Randagodron/satelyte/export/distortion_01_1.png

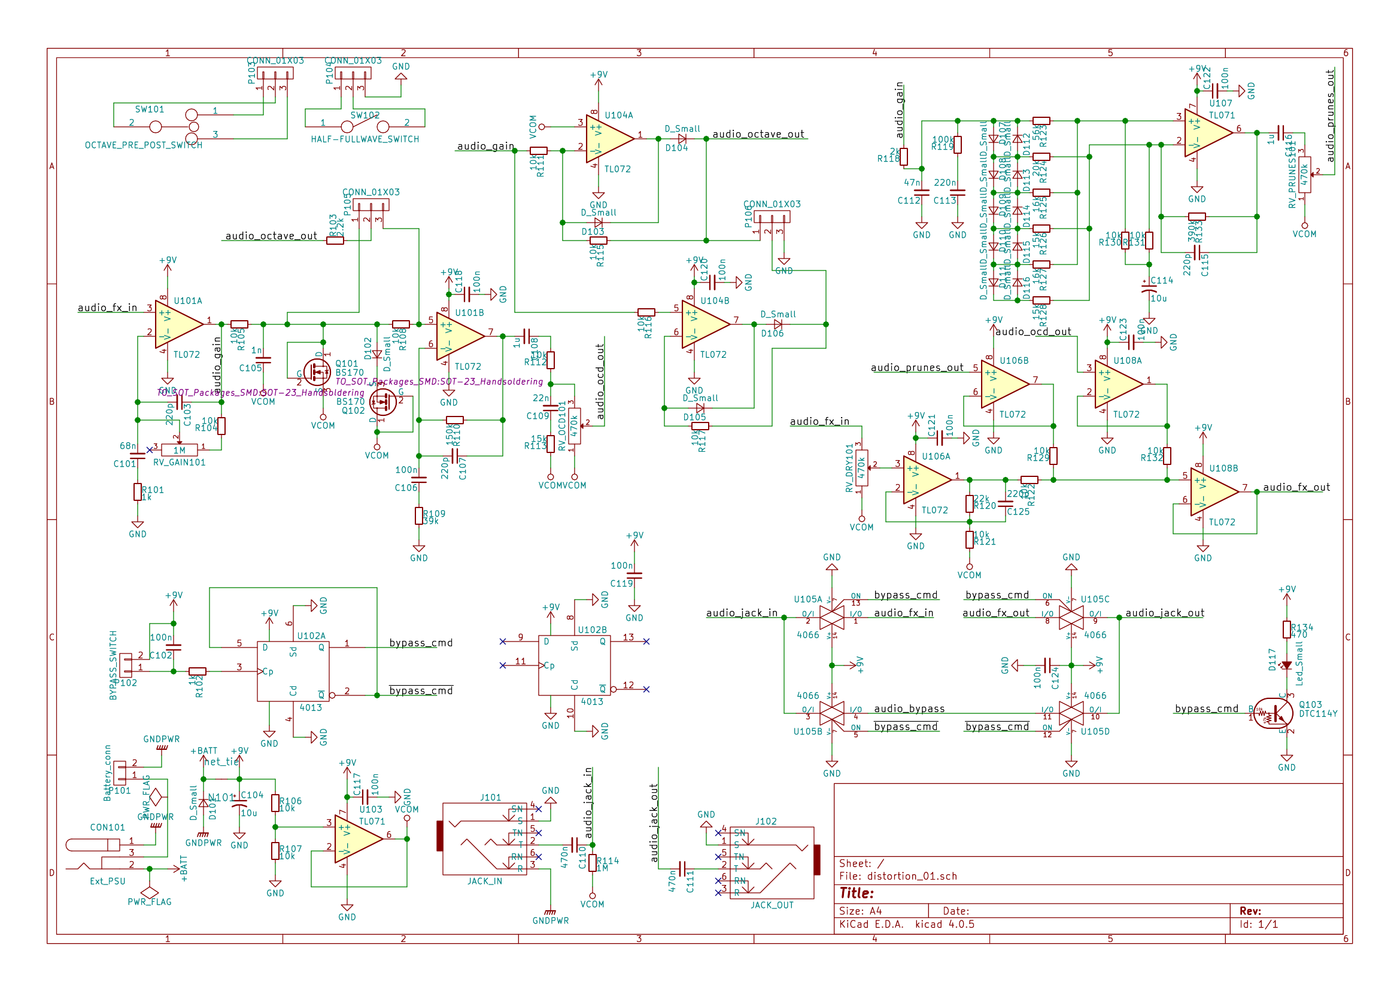
export/distortion_01_1.png
