Randagodron/satelyte/export/distortion_01_2.png

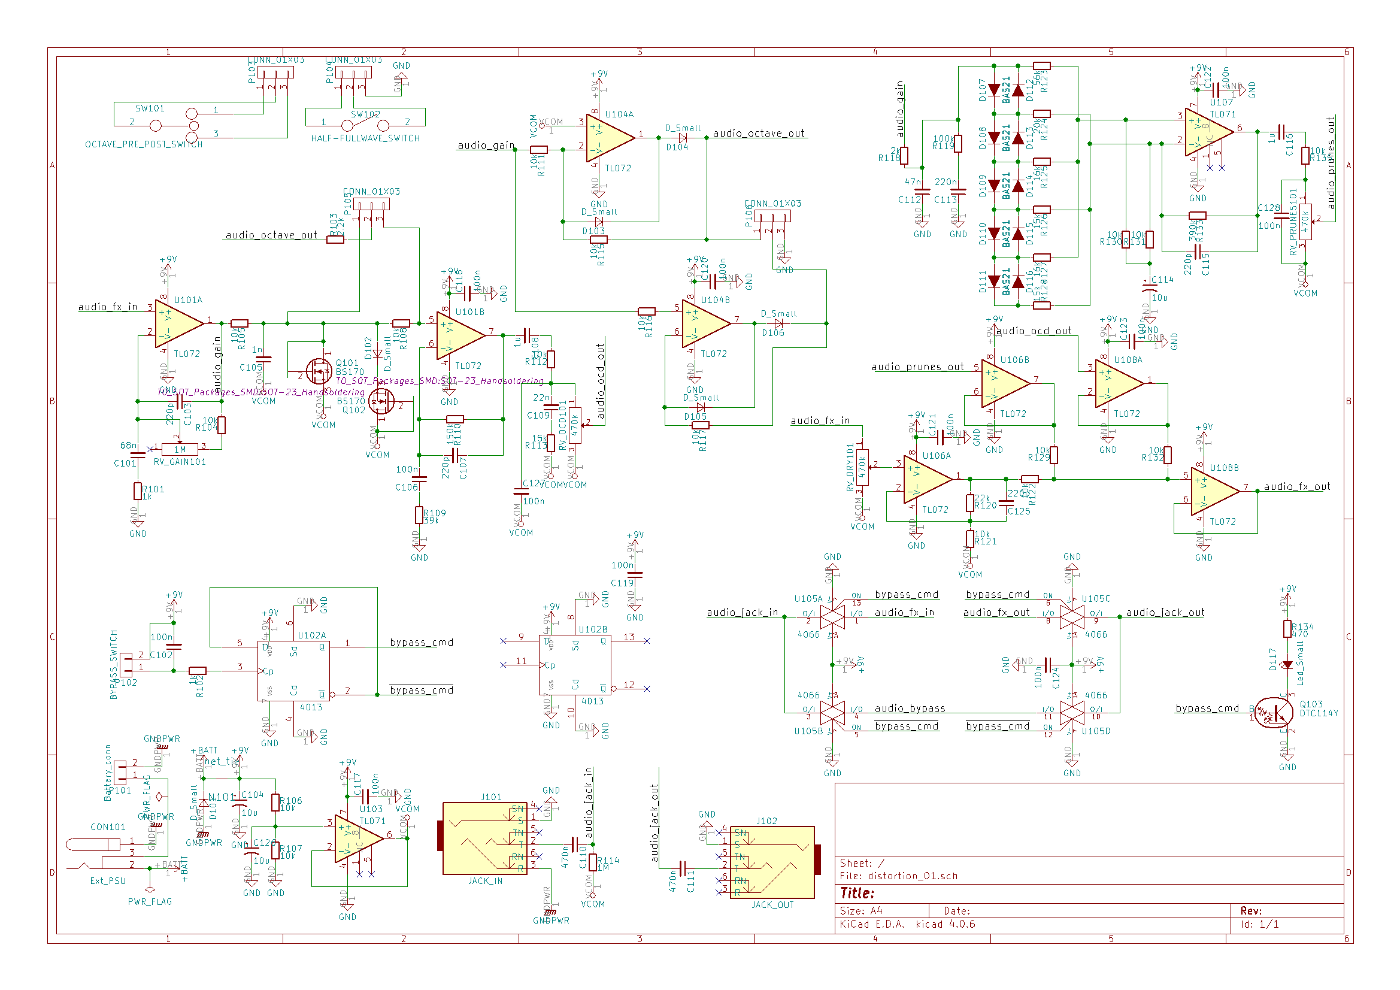
export/distortion_01_2.png
