Randagodron/satelyte/export/simu_schem_01_psu.PNG

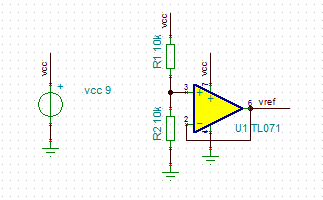
export/simu_schem_01_psu.PNG
