Randagodron/satelyte/export/simu_schem_02_octave.PNG

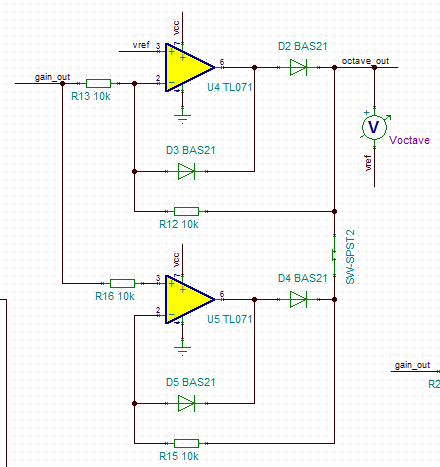
export/simu_schem_02_octave.PNG
