Randagodron/satelyte/export/simu_schem_03_ocd.PNG

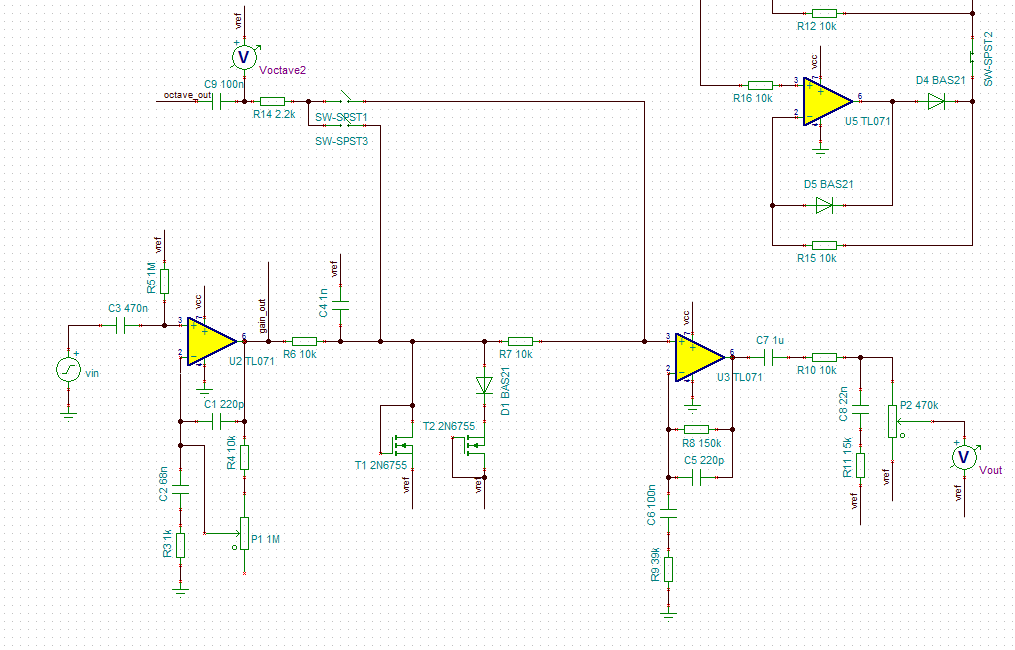
export/simu_schem_03_ocd.PNG
