Randagodron/satelyte/export/simu_schem_04_prunes.PNG

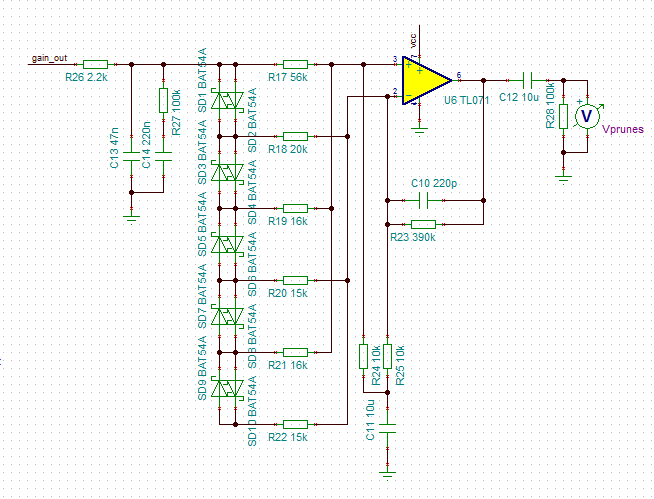
export/simu_schem_04_prunes.PNG
