Randagodron/satelyte/simu/distortion_01.asc

C1: cap; 1n
C2: cap; 1n
C3: cap; 68n
C4: cap; 470n
C5: cap; 220p
C6: cap; 100n
C7: cap; 1µ
C8: cap; 22n
C9: cap; 220n
C10: cap; 47n
C11: cap; 10µ
C12: cap; 1n
C13: cap; 1µ
D1: diode; 1N4148
D2: diode; 1N4148
D3: diode; 1N4148
D4: diode; 1N4148
D5: diode; 1N4148
D6: diode; 1N4148
D7: diode; 1N4148
D8: diode; 1N4148
D9: diode; 1N4148
D10: diode; 1N4148
D11: diode; 1N4148
D12: diode; 1N4148
D13: diode; 1N4148
D14: diode; 1N4148
D15: diode; 1N4148
R1: res; 10k
R2: res; 10k
R3: res; 10k
R4: res; {1MEG*GAIN}
R5: res; 1Meg
R6: res; 10k
R7: res; 150k
R8: res; 39k
R9: res; 10k
R10: res; 15k
R11: res; {100k*(1-VOL_OCD)}
R12: res; {100k*VOL_OCD}
R13: res; 10k
R14: res; 10k
R15: res; 10k
R16: res; 10k
R17: res; 2k
R18: res; 100k
R19: res; 56k
R20: res; 20k
R21: res; 16k
R22: res; 15k
R23: res; 16k
R24: res; 15k
R25: res; 10k
R26: res; 10k
R27: res; 390k
R28: res; {100k*(1-VOL_PRUNES)}
R29: res; {100k*VOL_PRUNES}
R30: res; 2.2k
U1: TL072
U2: TL072
U3: BS170
U4: BS170
U5: TL072
U6: TL072
U7: TL072
V1: voltage; 9
V2: voltage; 4.5
V3: voltage; SINE(0 100m 1k); AC 100m
Named nets: 0, vcc, vref, audio_out_ocd, audio_gain, audio_out_prunes
.param GAIN=0.5
.param VOL_OCD=0.5
;tran 200m
.param VOL_PRUNES=0.5
.ac oct 10 10 30k
